MarcelMG/DIY-Soldering-Station-Controller/firmware/tm1637.c

/**
 * Copyright (c) 2017-2018, Łukasz Marcin Podkalicki <lpodkalicki@gmail.com>
 * slightly modified by Marcel Meyer-Garcia to change pin settings easier via #define's
 * This is ATtiny13/25/45/85/24/44/84 library for 4-Digit LED Display based on TM1637 chip.
 *BSD 2-Clause License

 Copyright (c) 2017, Łukasz Podkalicki
 All rights reserved.

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
 * References:
 * - library: https://github.com/lpodkalicki/attiny-tm1637-library
 * - documentation: https://github.com/lpodkalicki/attiny-tm1637-library/README.md
 * - TM1637 datasheet: https://github.com/lpodkalicki/attiny-tm1637-library/blob/master/docs/TM1637_V2.4_EN.pdf
 */

#include <avr/io.h>
#include <avr/pgmspace.h>
#include <util/delay.h>
#include "tm1637.h"



static void TM1637_send_config(const uint8_t enable, const uint8_t brightness);
static void TM1637_send_command(const uint8_t value);
static void TM1637_start(void);
static void TM1637_stop(void);
static uint8_t TM1637_write_byte(uint8_t value);

static uint8_t _config = TM1637_SET_DISPLAY_ON | TM1637_BRIGHTNESS_MAX;
static uint8_t _segments = 0xff;
PROGMEM const uint8_t _digit2segments[] =
{
	0x3F, // 0
	0x06, // 1
	0x5B, // 2
	0x4F, // 3
	0x66, // 4
	0x6D, // 5
	0x7D, // 6
	0x07, // 7
	0x7F, // 8
	0x6F  // 9
};

void
TM1637_init(const uint8_t enable, const uint8_t brightness)
{

	TM1637_DIO_OUTPUT();
	TM1637_CLK_OUTPUT();
	TM1637_DIO_LOW();
	TM1637_CLK_LOW();
	TM1637_send_config(enable, brightness);
}

void
TM1637_enable(const uint8_t value)
{

	TM1637_send_config(value, _config & TM1637_BRIGHTNESS_MAX);
}

void
TM1637_set_brightness(const uint8_t value)
{

	TM1637_send_config(_config & TM1637_SET_DISPLAY_ON,
		value & TM1637_BRIGHTNESS_MAX);
}

void
TM1637_display_segments(const uint8_t position, const uint8_t segments)
{
	TM1637_send_command(TM1637_CMD_SET_DATA | TM1637_SET_DATA_F_ADDR);
	TM1637_start();
	TM1637_write_byte(TM1637_CMD_SET_ADDR | (position & (TM1637_POSITION_MAX - 1)));
	TM1637_write_byte(segments);
	TM1637_stop();
}

void
TM1637_display_digit(const uint8_t position, const uint8_t digit)
{
	uint8_t segments = (digit < 10 ? pgm_read_byte_near((uint8_t *)&_digit2segments + digit) : 0x00);

	if (position == 0x01) {
		segments = segments | (_segments & 0x80);
		_segments = segments;
	}

	TM1637_display_segments(position, segments);
}

void
TM1637_display_colon(const uint8_t value)
{

	if (value) {
		_segments |= 0x80;
	} else {
		_segments &= ~0x80;
	}
	TM1637_display_segments(0x01, _segments);
}

void
TM1637_clear(void)
{
	uint8_t i;

	for (i = 0; i < TM1637_POSITION_MAX; ++i) {
		TM1637_display_segments(i, 0x00);
	}
}

void
TM1637_send_config(const uint8_t enable, const uint8_t brightness)
{

	_config = (enable ? TM1637_SET_DISPLAY_ON : TM1637_SET_DISPLAY_OFF) |
		(brightness > TM1637_BRIGHTNESS_MAX ? TM1637_BRIGHTNESS_MAX : brightness);

	TM1637_send_command(TM1637_CMD_SET_DSIPLAY | _config);
}

void
TM1637_send_command(const uint8_t value)
{

	TM1637_start();
	TM1637_write_byte(value);
	TM1637_stop();
}

void
TM1637_start(void)
{

	TM1637_DIO_HIGH();
	TM1637_CLK_HIGH();
	_delay_us(TM1637_DELAY_US);
	TM1637_DIO_LOW();
}

void
TM1637_stop(void)
{

	TM1637_CLK_LOW();
	_delay_us(TM1637_DELAY_US);

	TM1637_DIO_LOW();
	_delay_us(TM1637_DELAY_US);

	TM1637_CLK_HIGH();
	_delay_us(TM1637_DELAY_US);

	TM1637_DIO_HIGH();
}

uint8_t
TM1637_write_byte(uint8_t value)
{
	uint8_t i, ack;

	for (i = 0; i < 8; ++i, value >>= 1) {
		TM1637_CLK_LOW();
		_delay_us(TM1637_DELAY_US);

		if (value & 0x01) {
			TM1637_DIO_HIGH();
		} else {
			TM1637_DIO_LOW();
		}

		TM1637_CLK_HIGH();
		_delay_us(TM1637_DELAY_US);
	}

	TM1637_CLK_LOW();
	TM1637_DIO_INPUT();
	TM1637_DIO_HIGH();
	_delay_us(TM1637_DELAY_US);

	ack = TM1637_DIO_READ();
	if (ack) {
		TM1637_DIO_OUTPUT();
		TM1637_DIO_LOW();
	}
	_delay_us(TM1637_DELAY_US);

	TM1637_CLK_HIGH();
	_delay_us(TM1637_DELAY_US);

	TM1637_CLK_LOW();
	_delay_us(TM1637_DELAY_US);

	TM1637_DIO_OUTPUT();

	return ack;
}
